liulizhi1031/MyOECU/3D_model/ComputTower/配电模块.SLDPRT

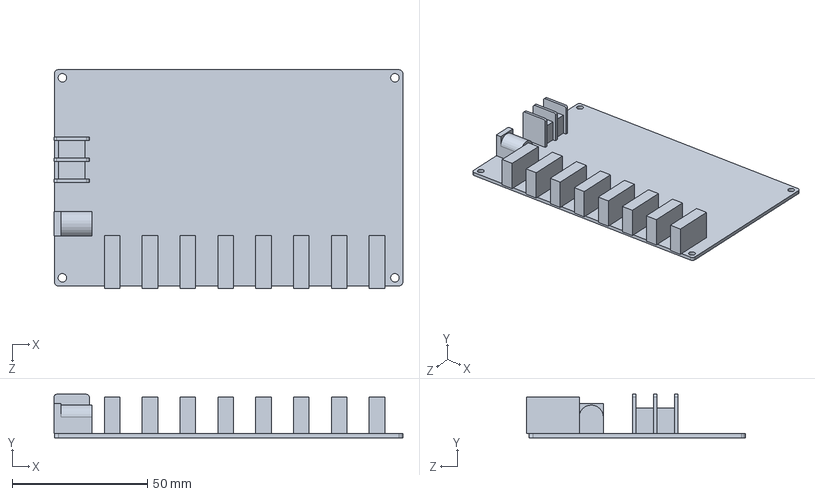
[picture p30: CAD file, 2023-07-12]
3D_model/ComputTower/配电模块.SLDPRT
129.1 x 16.1 x 80.9 mm
