liulizhi1031/MyOECU/3D_model/OLED.SLDPRT

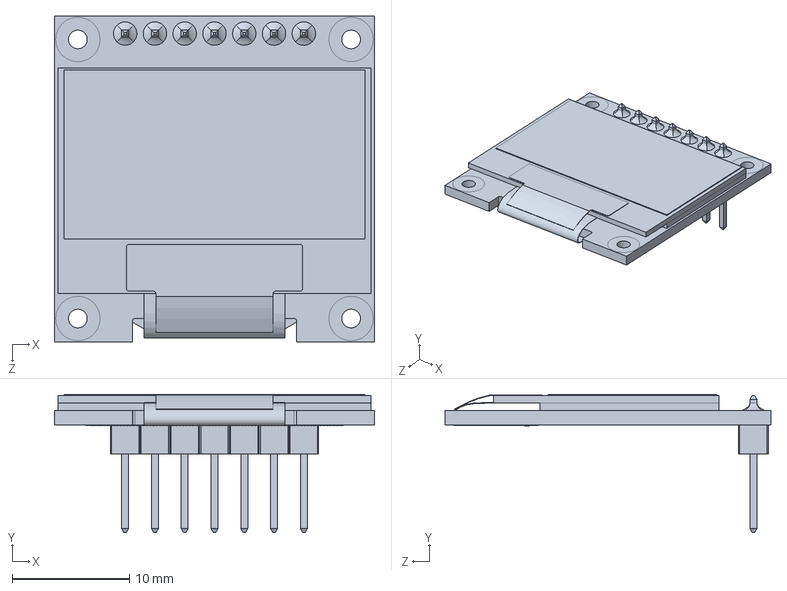
[picture p31: CAD file, 2023-04-11]
3D_model/OLED.SLDPRT
27.3 x 11.8 x 27.8 mm
