liulizhi1031/MyOECU/3D_model/PinSocket7_2.54.SLDPRT

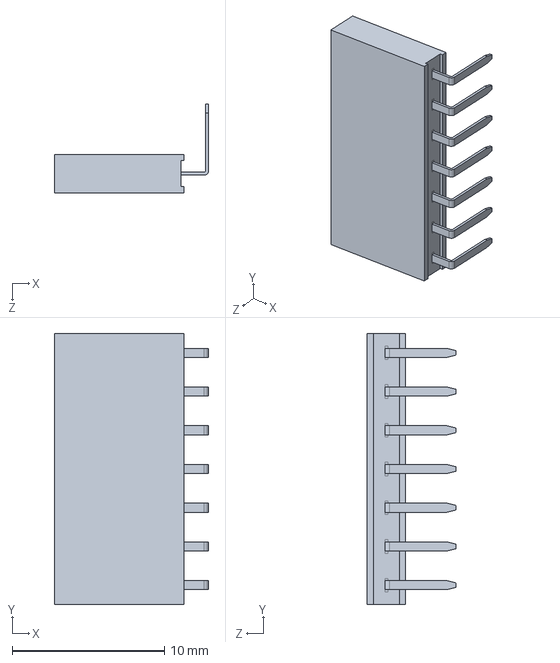
[picture p32: CAD file, 2023-04-11]
3D_model/PinSocket7_2.54.SLDPRT
10.1 x 17.8 x 5.84 mm
