liulizhi1031/MyOECU/3D_model/ZYNQ_CORE.SLDPRT

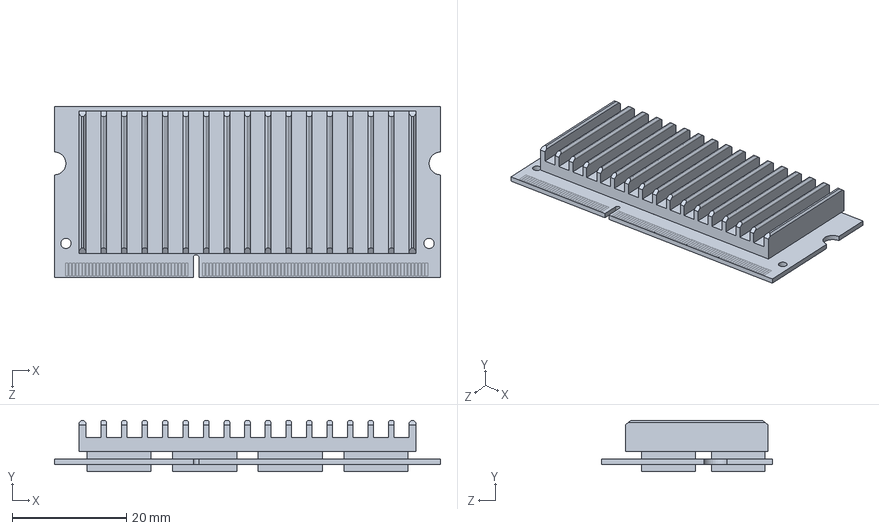
[picture p33: CAD file, 2022-12-28]
3D_model/ZYNQ_CORE.SLDPRT
67.6 x 9.00 x 30.0 mm
