liulizhi1031/MyOECU/doc/Zynq/COR_ZYNQ_DDR3V2.1装配图.pdf

# ART FILM - ADT

U19R7

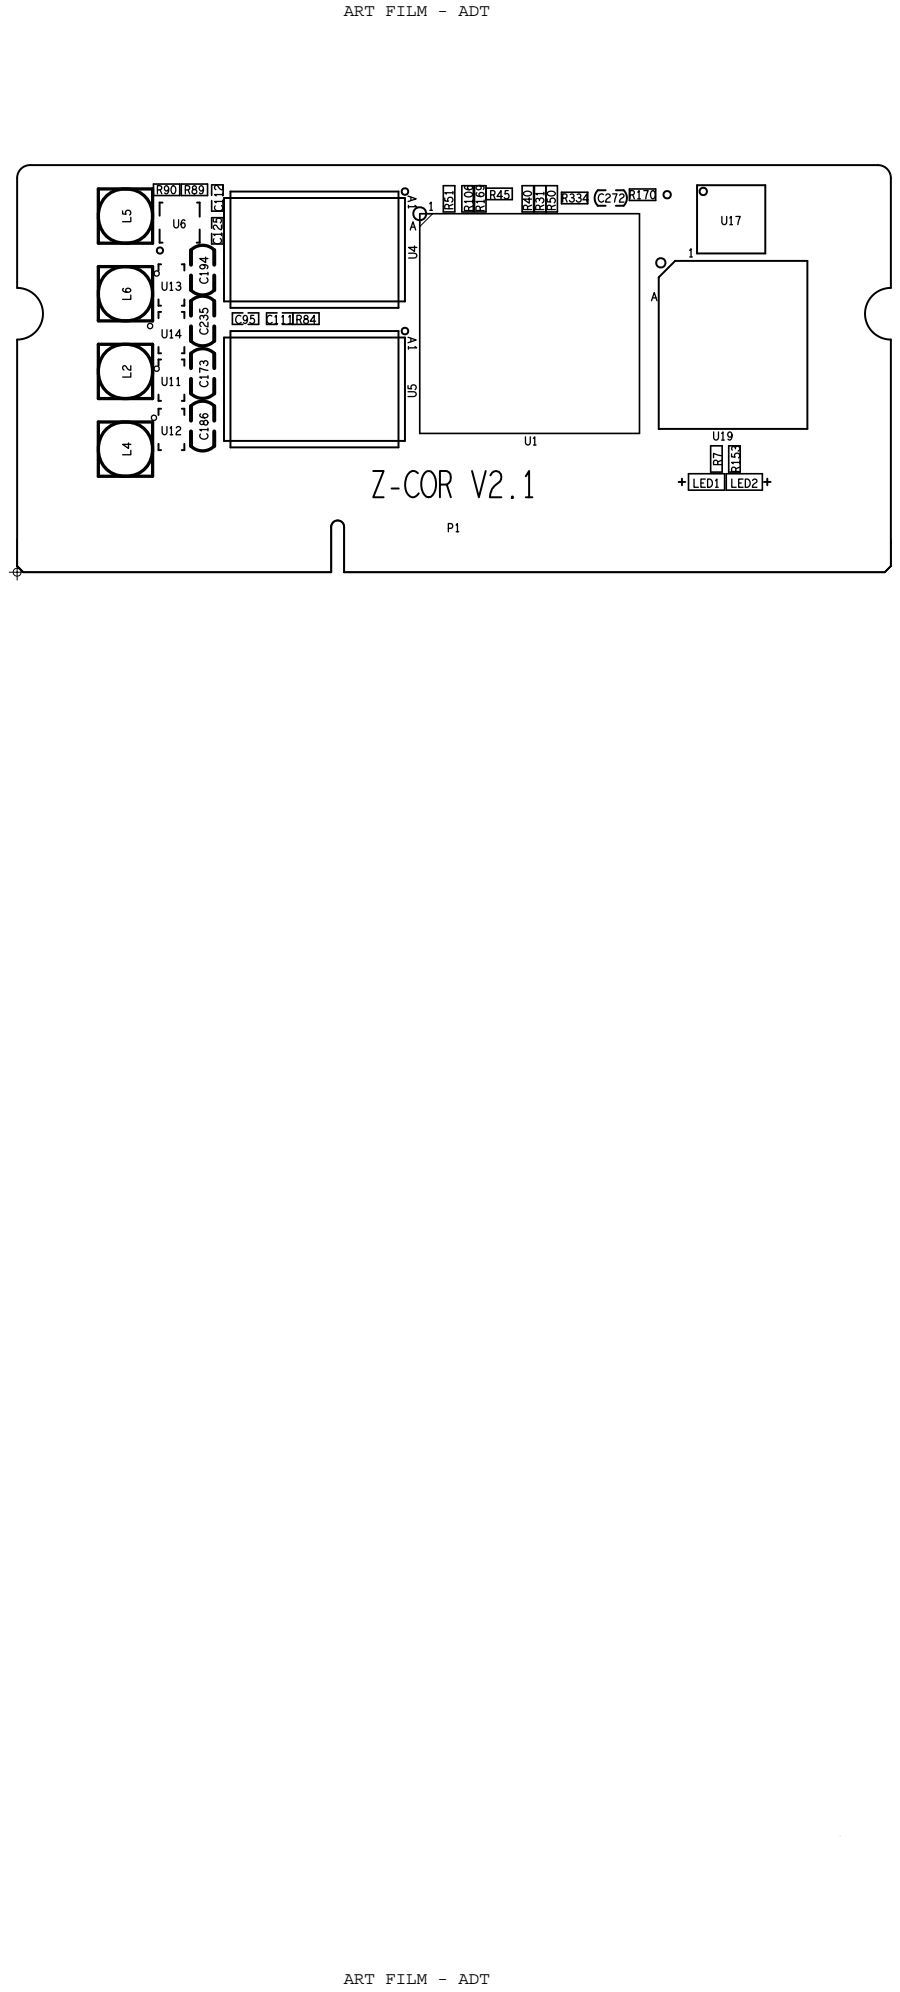
[picture p37: page 1]

# ART FILM - ADB

C117R77

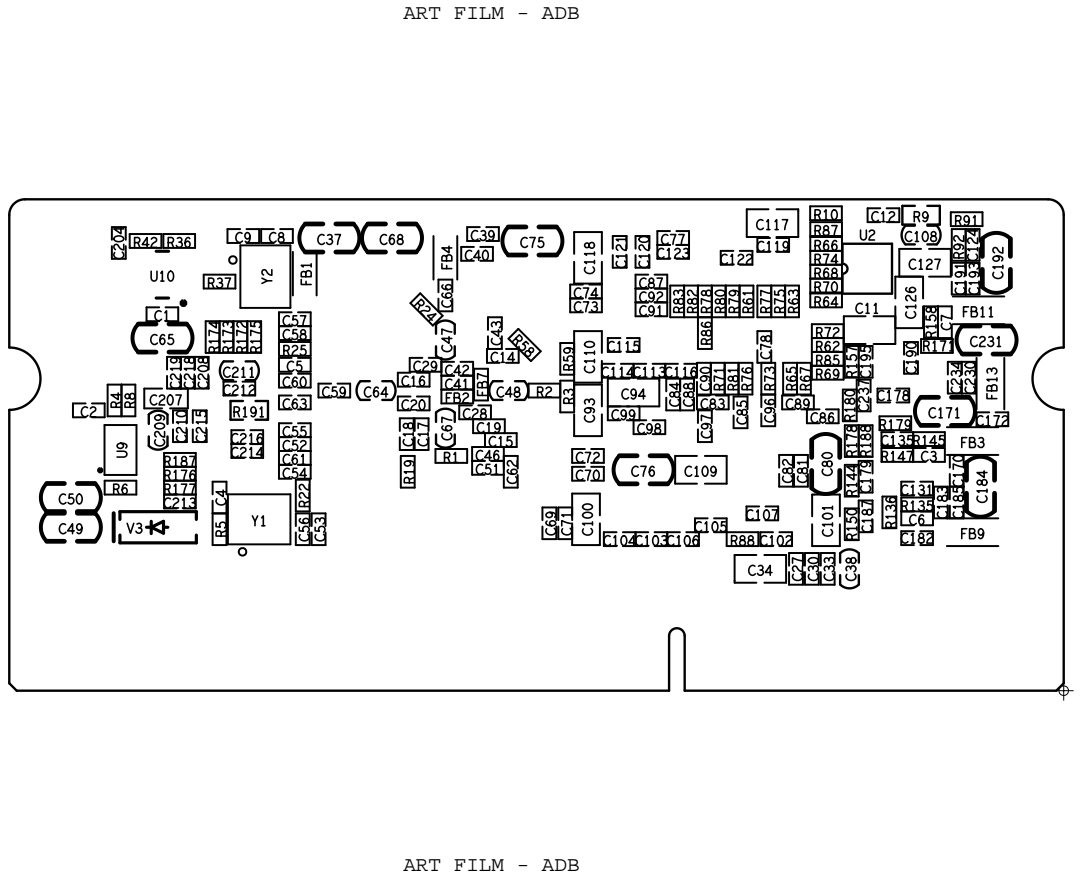
[picture p38: page 2]
