liulizhi1031/MyOECU/pcb/OECU_BASE/OECU_BASE.pdf

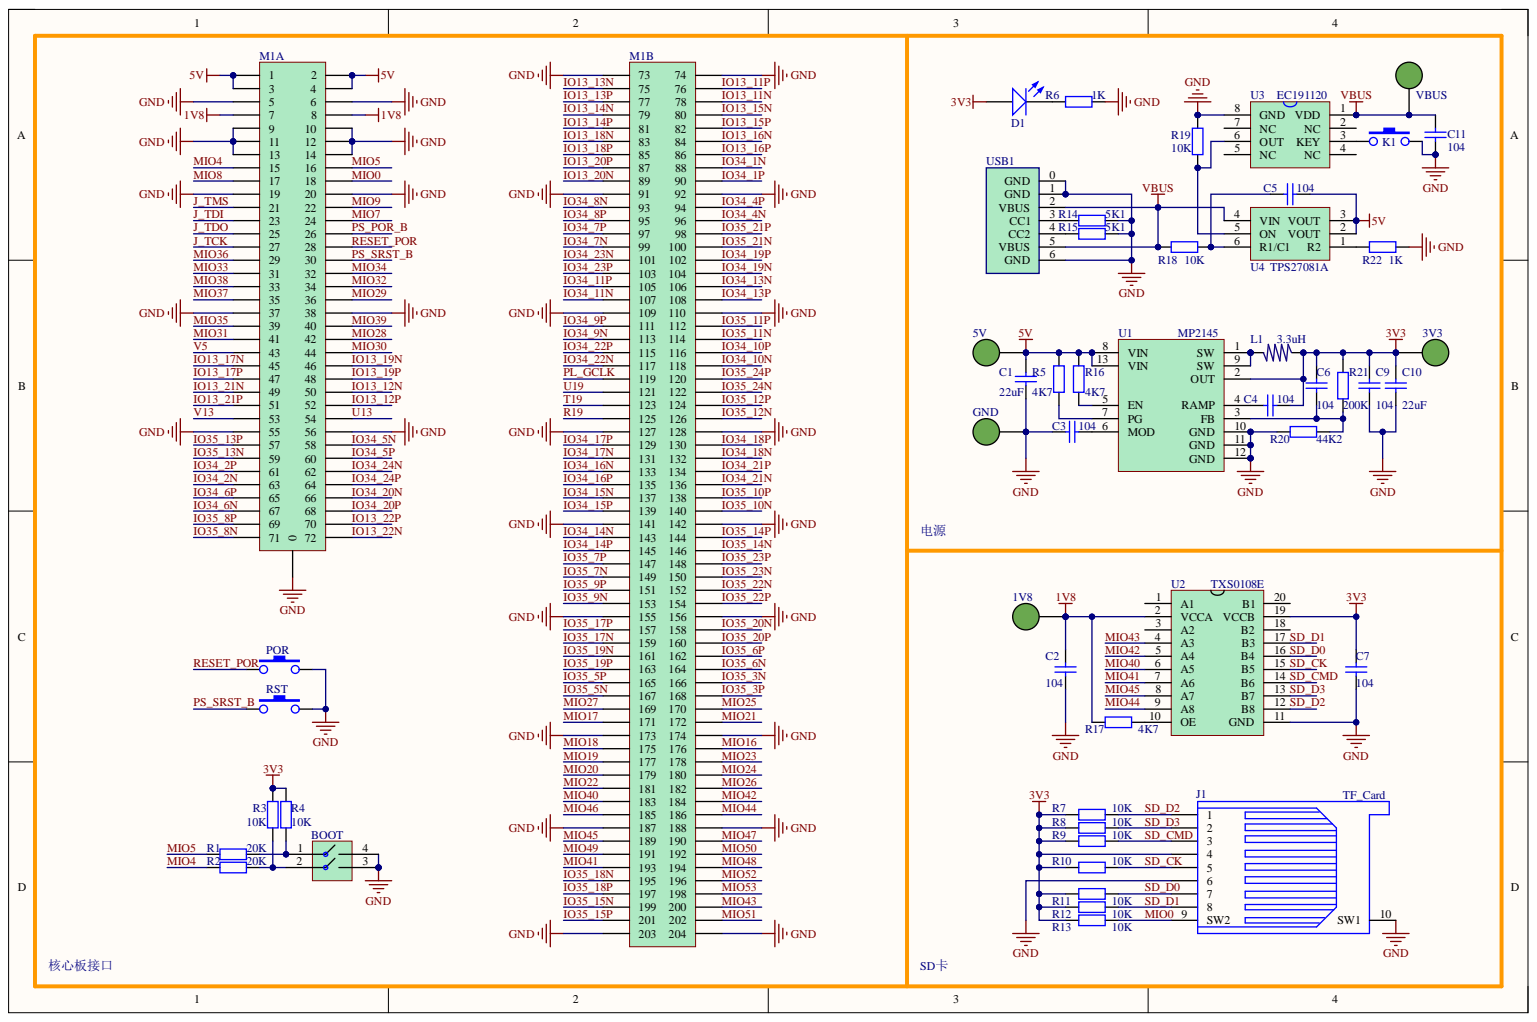
[picture p39: page 1]

2 0 K

R1 1 | | 1 0 K SD _D | 1
R1 | 2 | | 1 0 K MIO | 0

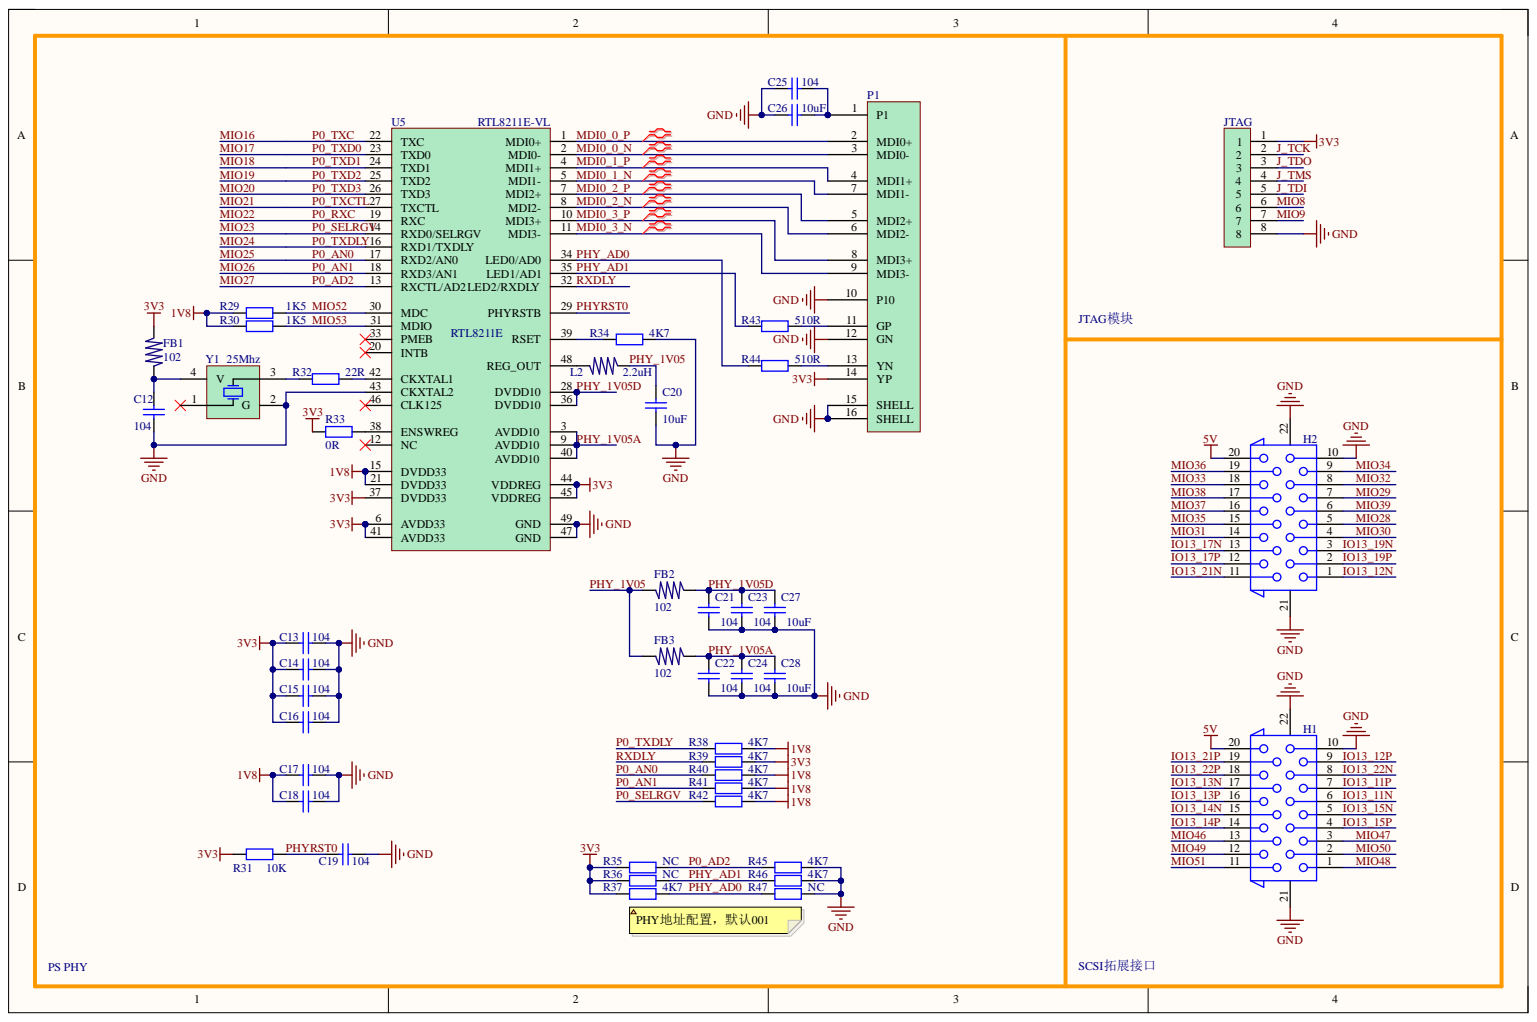
[picture p40: page 2]

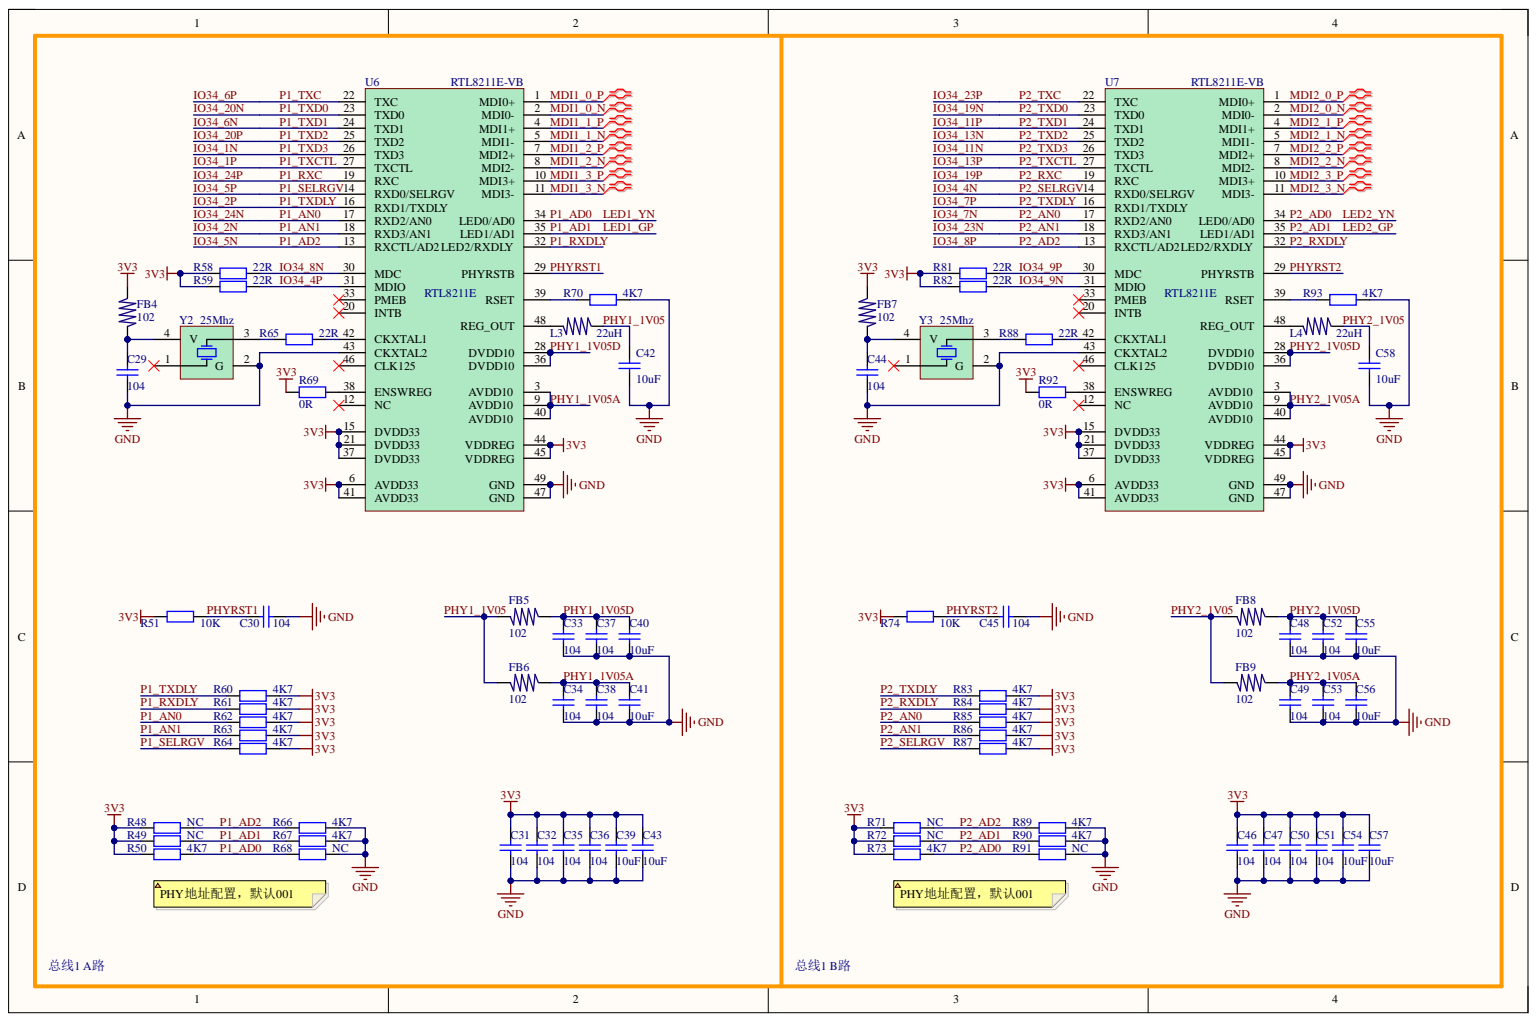
[picture p41: page 3]

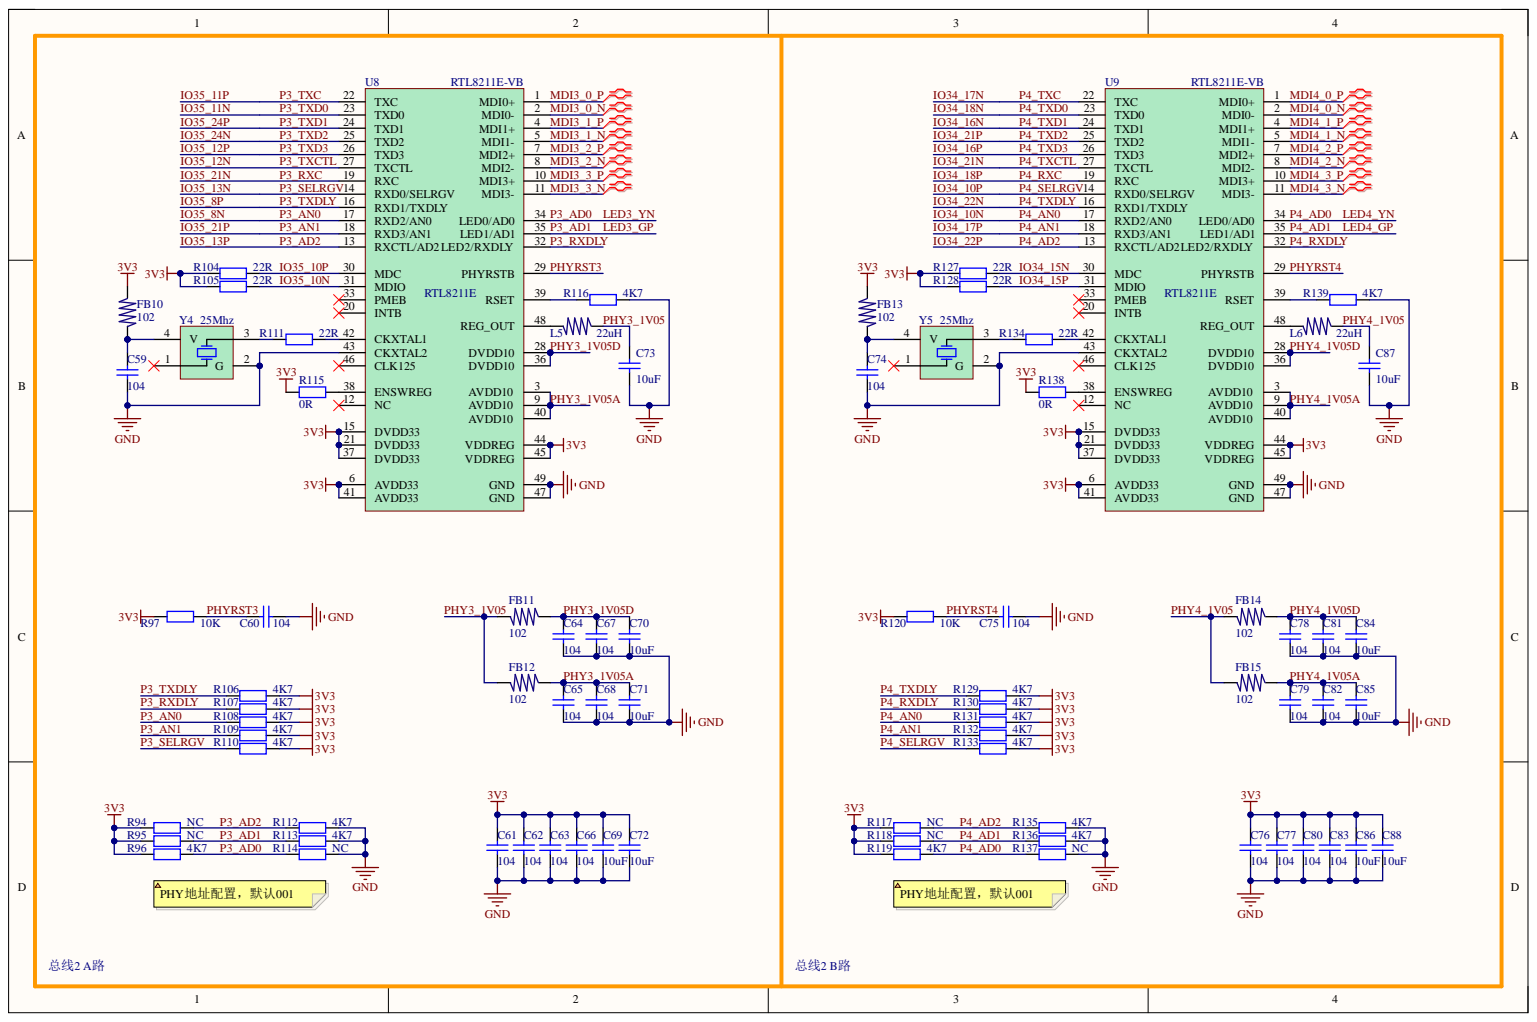
[picture p42: page 4]

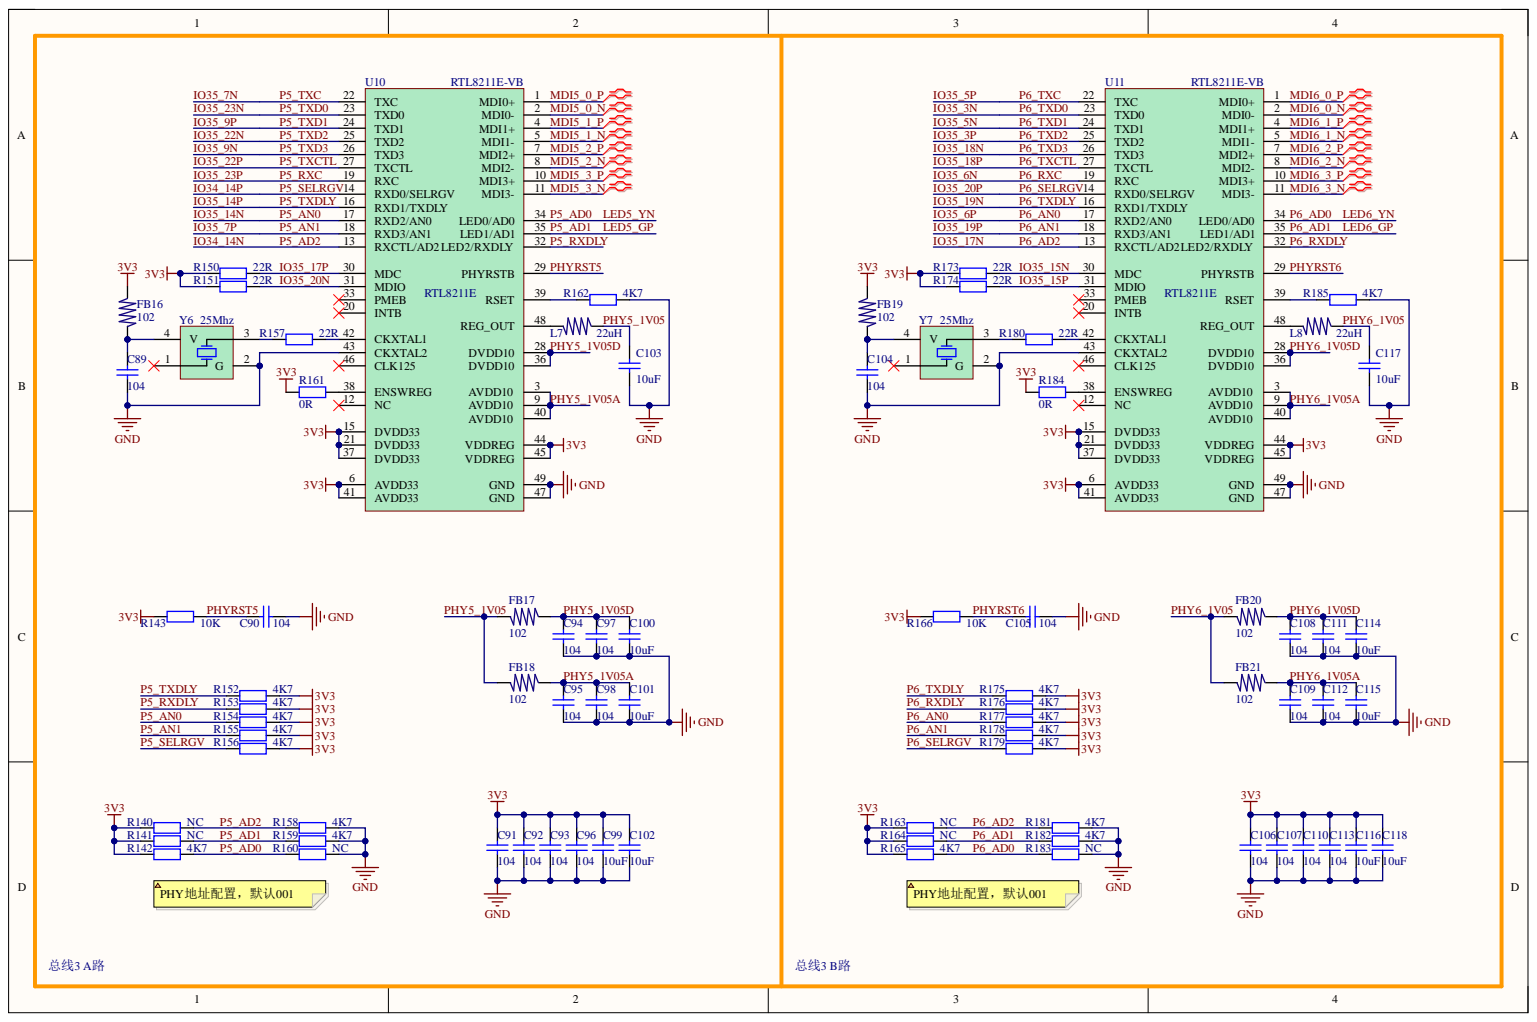
[picture p43: page 5]

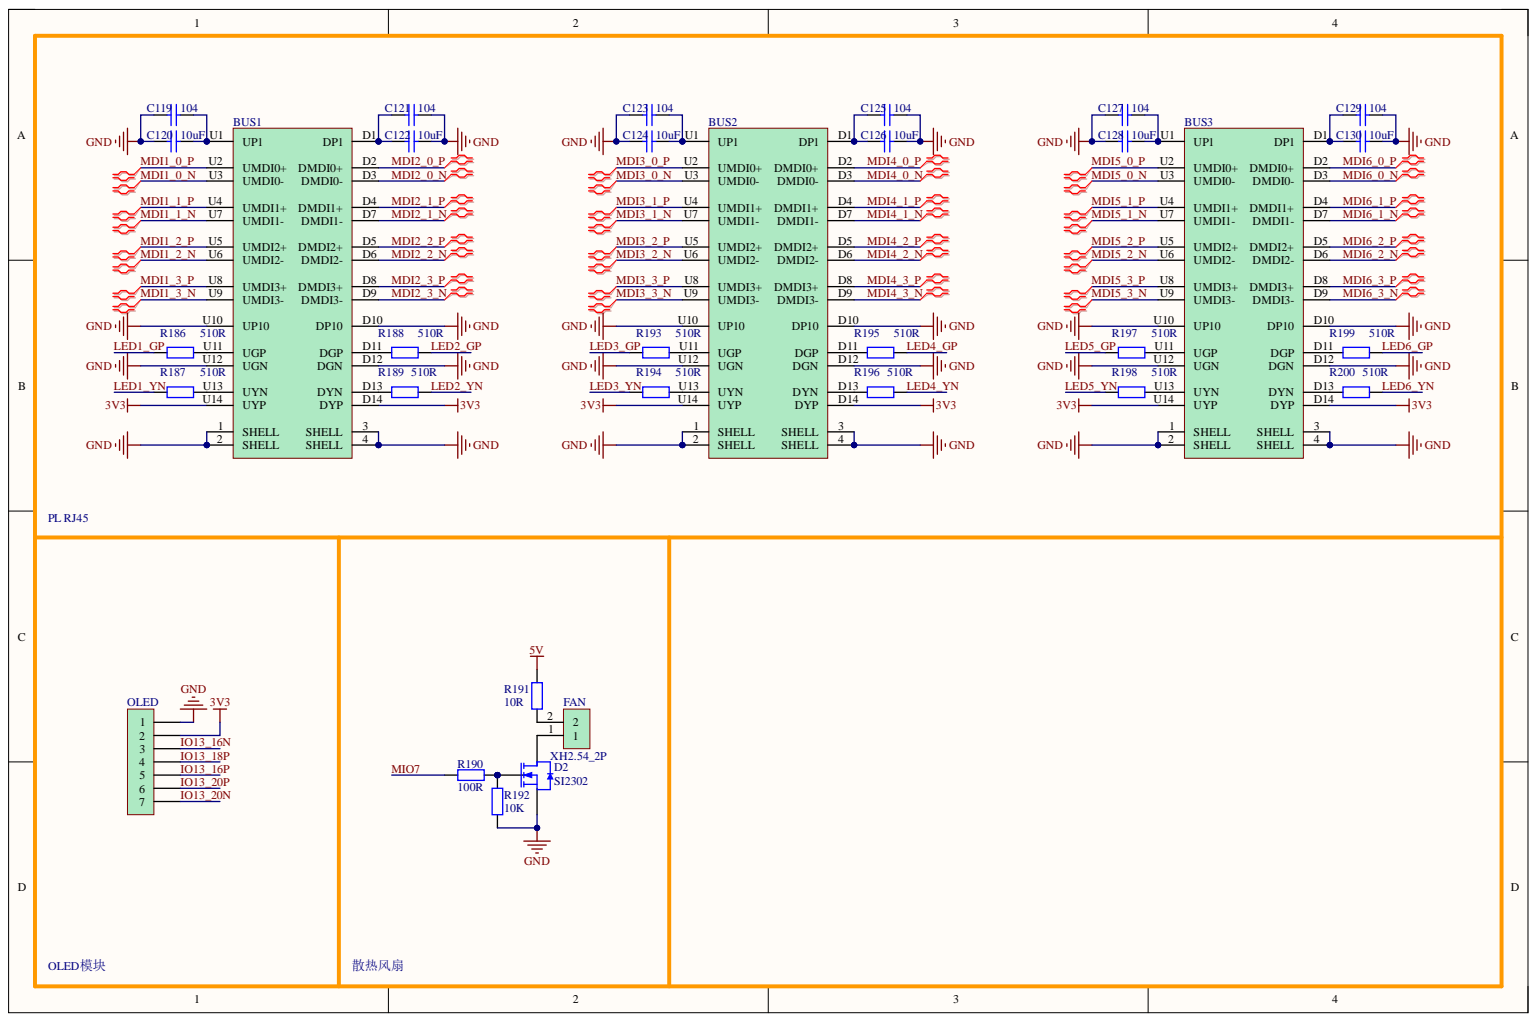
[picture p44: page 6]
