liulizhi1031/MyOECU/doc/Zynq/底板V3ZBOARD原理图.pdf

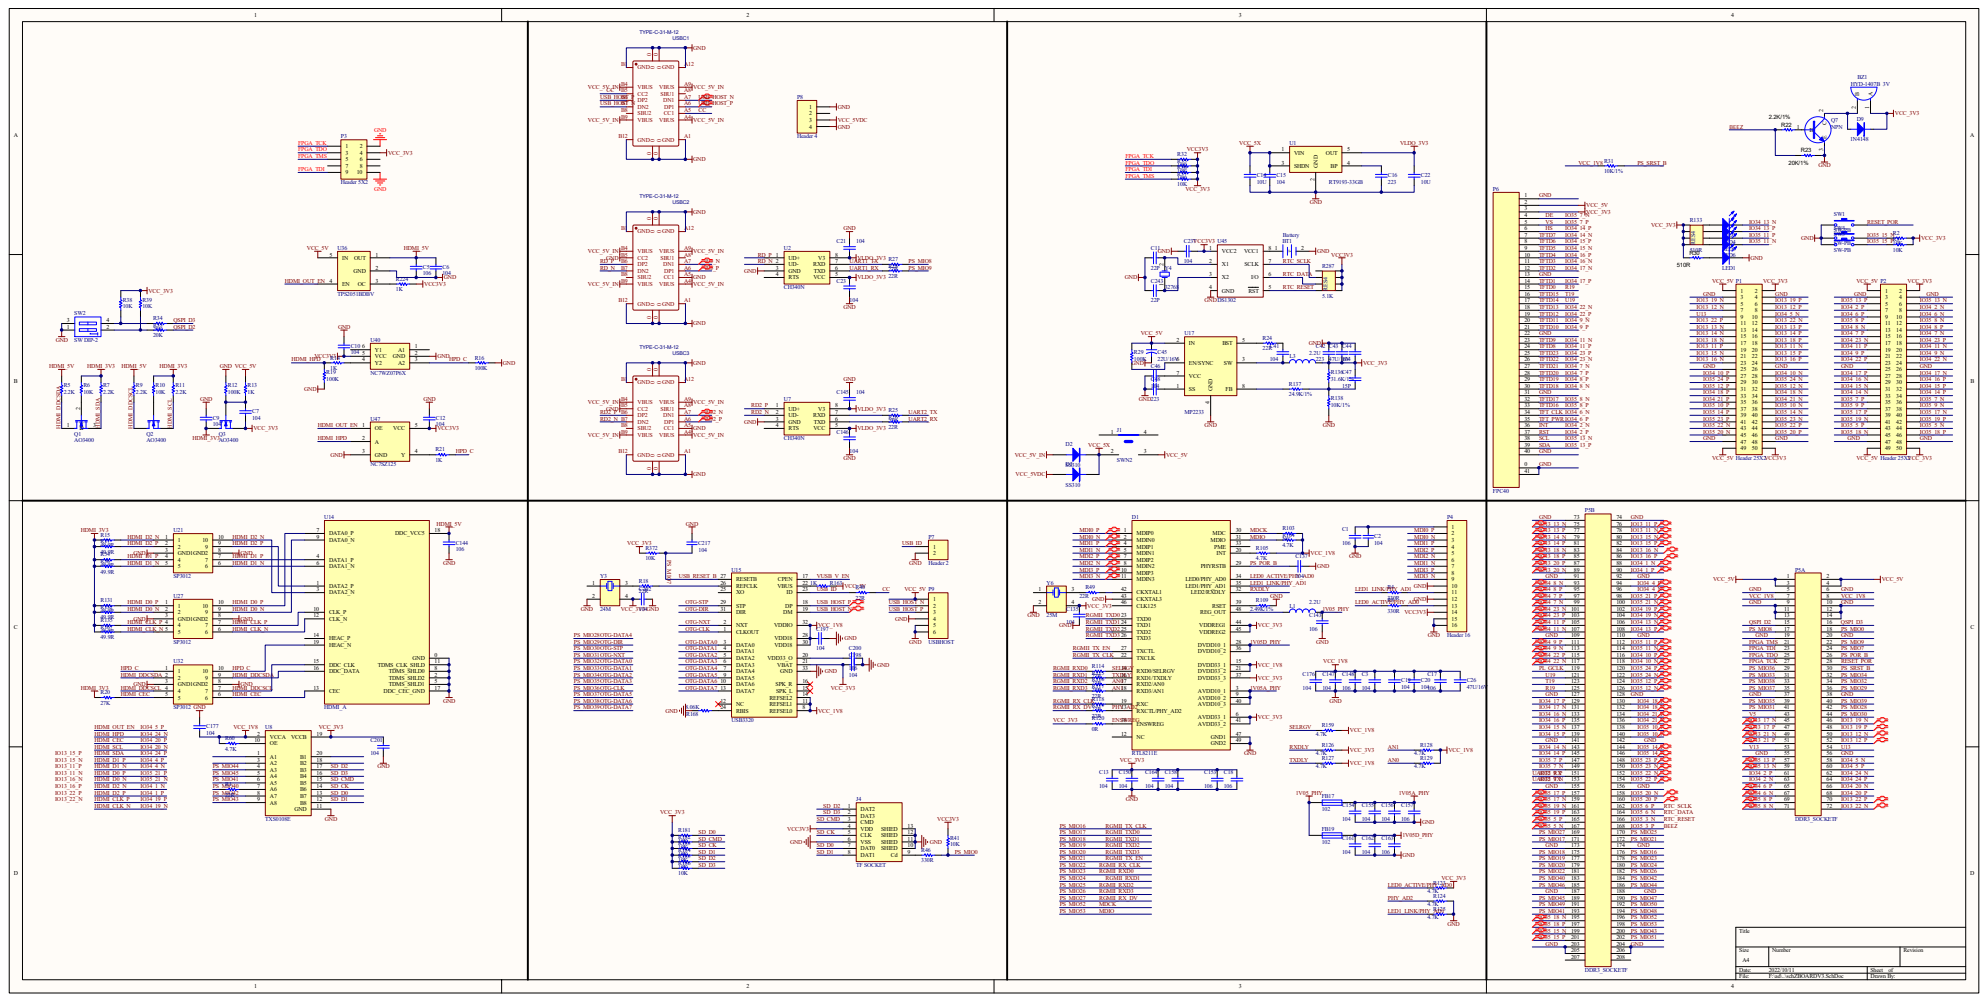
[picture p45: page 1]
