liulizhi1031/MyOECU/doc/Zynq/SCH_COR_ZYNQvV2.1.pdf

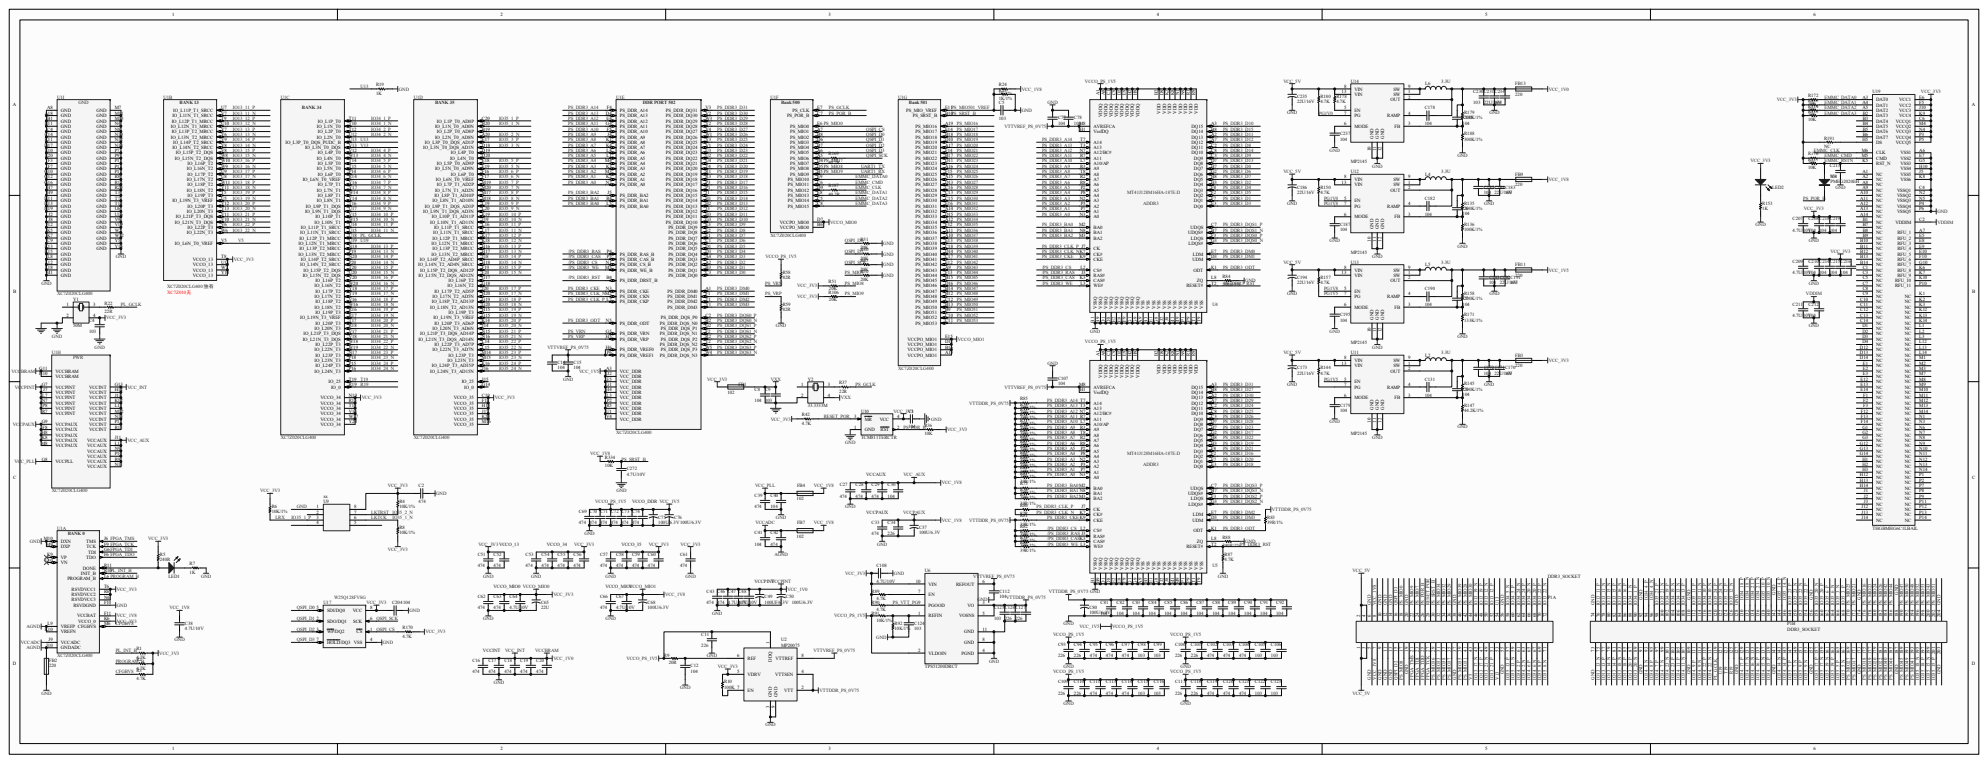
[picture p46: page 1]
